starlightk7/OpenSFC/Sound Modules/TCMK-77XR F/Rev B/TCMK-77XR.kicad_sch

## KiCad design Sound Modules/TCMK-77XR F/Rev B/TCMK-77XR.kicad_sch (2026-03-24)

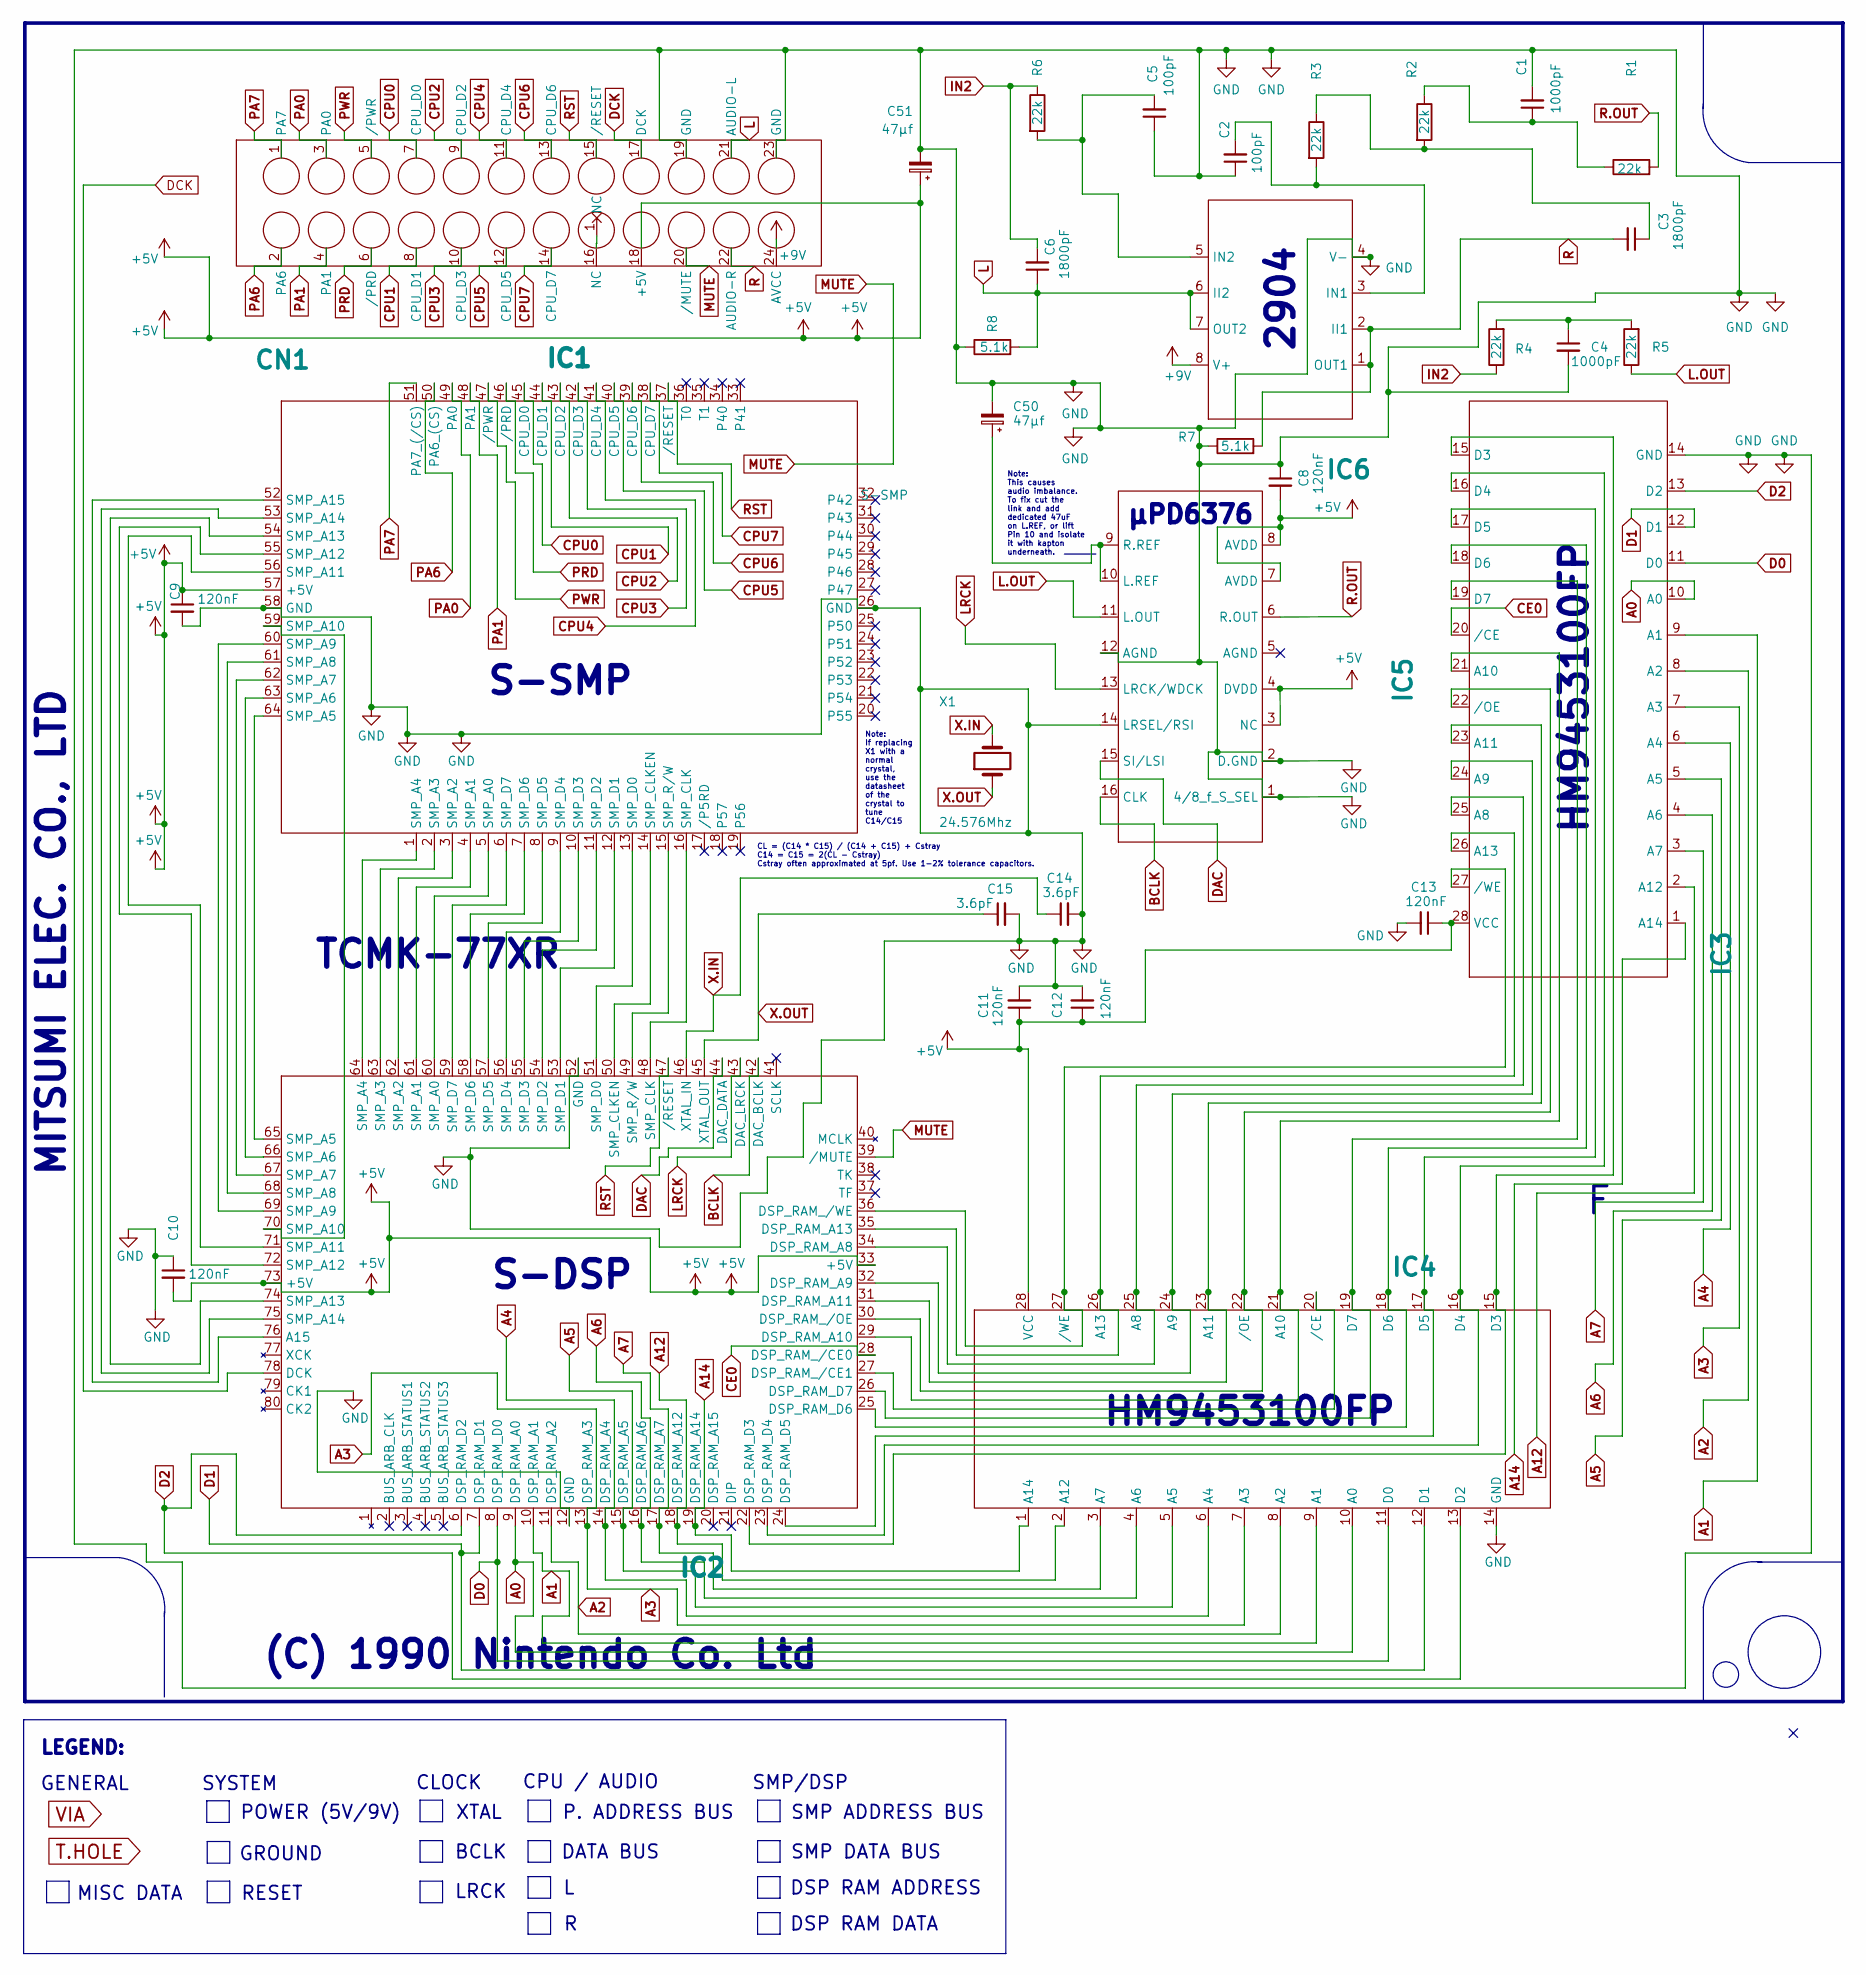
[picture p21: schematic TCMK-77XR.kicad_sch]

Parts:
C1, C4: 1000pF; C_0805_2012Metric
C2, C5: 100pF; C_0805_2012Metric
C3, C6: 1800pF; C_0805_2012Metric
C8, C9, C10, C11, C12, C13: 120nF; C_0805_2012Metric
C14, C15: 3.6pF; C_0805_2012Metric
C50, C51: 47µf; C_Radial_D6.3mm_H5.0mm_P2.50mm
CN1: 2x12 Connector Female; PinHeader_2x12_P2.00mm_Vertical
IC1: S-SMP
IC2: S-DSP
IC3, IC4: HM9453100FP; SOP-28_8.4x18.16mm_P1.27mm
IC5: µPD6376; SOIC-16W_7.5x10.3mm_P1.27mm
IC6: 2904; SOIC-8_3.9x4.9mm_P1.27mm
R1, R2, R3, R4, R5, R6: 22k; R_0805_2012Metric
R7, R8: 5.1k; R_0805_2012Metric
U99: NCStub
X1: 24.576Mhz; Crystal_HC18-U_Vertical

Connections:
+5V: C8.2, C9.1, C10.2, C11.1, C12.1, C13.1, C51.1, CN1.18 (+5V), IC1.57 (+5V), IC2.33 (+5V), IC2.73 (+5V), IC3.28 (VCC), IC4.28 (VCC), IC5.3 (NC), IC5.4 (DVDD), IC5.7 (AVDD), IC5.8 (AVDD)
+9V: CN1.24 (AVCC), IC6.8 (V+)
A0: IC2.9 (DSP_RAM_A0), IC3.10 (A0), IC4.10 (A0)
A1: IC2.10 (DSP_RAM_A1), IC3.9 (A1), IC4.9 (A1)
A2: IC2.11 (DSP_RAM_A2), IC3.8 (A2), IC4.8 (A2)
A3: IC2.13 (DSP_RAM_A3), IC3.7 (A3), IC4.7 (A3)
A4: IC2.14 (DSP_RAM_A4), IC3.6 (A4), IC4.6 (A4)
A5: IC2.15 (DSP_RAM_A5), IC3.5 (A5), IC4.5 (A5)
A6: IC2.16 (DSP_RAM_A6), IC3.4 (A6), IC4.4 (A6)
A7: IC2.17 (DSP_RAM_A7), IC3.3 (A7), IC4.3 (A7)
A12: IC2.18 (DSP_RAM_A12), IC3.2 (A12), IC4.2 (A12)
A14: IC2.19 (DSP_RAM_A14), IC3.1 (A14), IC4.1 (A14)
BCLK: IC2.42 (DAC_BCLK), IC5.16 (CLK)
CE0: IC2.28 (DSP_RAM_/CE0), IC3.20 (/CE)
CPU0: CN1.7 (CPU_D0), IC1.45 (CPU_D0)
CPU1: CN1.8 (CPU_D1), IC1.44 (CPU_D1)
CPU2: CN1.9 (CPU_D2), IC1.43 (CPU_D2)
CPU3: CN1.10 (CPU_D3), IC1.42 (CPU_D3)
CPU4: CN1.11 (CPU_D4), IC1.41 (CPU_D4)
CPU5: CN1.12 (CPU_D5), IC1.40 (CPU_D5)
CPU6: CN1.13 (CPU_D6), IC1.39 (CPU_D6)
CPU7: CN1.14 (CPU_D7), IC1.38 (CPU_D7)
D0: IC2.8 (DSP_RAM_D0), IC3.11 (D0), IC4.11 (D0)
D1: IC2.7 (DSP_RAM_D1), IC3.12 (D1), IC4.12 (D1)
D2: IC2.6 (DSP_RAM_D2), IC3.13 (D2), IC4.13 (D2)
DAC: IC2.44 (DAC_DATA), IC5.15 (SI/LSI)
DCK: CN1.17 (DCK), IC2.78 (DCK)
GND: C1.2, C2.1, C4.2, C5.1, C8.1, C9.2, C10.1, C11.2, C12.2, C13.2, C14.2, C15.2, C50.2, C51.2, CN1.19 (GND), CN1.23 (GND), IC1.26 (GND), IC1.58 (GND), IC2.12 (GND), IC2.52 (GND), IC3.14 (GND), IC4.14 (GND), IC5.1 (4/8_f_S_SEL), IC5.2 (D.GND), IC5.12 (AGND), IC5.14 (LRSEL/RSI), IC6.4 (V-), R7.1, R8.1
IN2: C6.2, R4.1, R6.1
L: C6.1, CN1.21 (AUDIO-L), IC6.6 (II2), IC6.7 (OUT2), R8.2
L.OUT: IC5.11 (L.OUT), R5.1
LRCK: IC2.43 (DAC_LRCK), IC5.13 (LRCK/WDCK)
MUTE: CN1.20 (/MUTE), IC2.39 (/MUTE)
unnamed: C1.1, R1.1, R2.1
unnamed: C2.2, IC6.3 (IN1), R3.2
unnamed: C3.1, R2.2, R3.1
unnamed: C4.1, R4.2, R5.2
unnamed: C5.2, IC6.5 (IN2), R6.2
unnamed: C50.1, IC5.9 (R.REF), IC5.10 (L.REF)
unnamed: CN1.16 (NC), U99.1
unnamed: IC1.1 (SMP_A4), IC2.64 (SMP_A4)
unnamed: IC1.2 (SMP_A3), IC2.63 (SMP_A3)
unnamed: IC1.3 (SMP_A2), IC2.62 (SMP_A2)
unnamed: IC1.4 (SMP_A1), IC2.61 (SMP_A1)
unnamed: IC1.5 (SMP_A0), IC2.60 (SMP_A0)
unnamed: IC1.6 (SMP_D7), IC2.59 (SMP_D7)
unnamed: IC1.7 (SMP_D6), IC2.58 (SMP_D6)
unnamed: IC1.8 (SMP_D5), IC2.57 (SMP_D5)
unnamed: IC1.9 (SMP_D4), IC2.56 (SMP_D4)
unnamed: IC1.10 (SMP_D3), IC2.55 (SMP_D3)
unnamed: IC1.11 (SMP_D2), IC2.54 (SMP_D2)
unnamed: IC1.12 (SMP_D1), IC2.53 (SMP_D1)
unnamed: IC1.13 (SMP_D0), IC2.51 (SMP_D0)
unnamed: IC1.14 (SMP_CLKEN), IC2.50 (SMP_CLKEN)
unnamed: IC1.15 (SMP_R/W), IC2.49 (SMP_R/W)
unnamed: IC1.16 (SMP_CLK), IC2.48 (SMP_CLK)
unnamed: IC1.52 (SMP_A15), IC2.76 (A15)
unnamed: IC1.53 (SMP_A14), IC2.75 (SMP_A14)
unnamed: IC1.54 (SMP_A13), IC2.74 (SMP_A13)
unnamed: IC1.55 (SMP_A12), IC2.72 (SMP_A12)
unnamed: IC1.56 (SMP_A11), IC2.71 (SMP_A11)
unnamed: IC1.59 (SMP_A10), IC2.70 (SMP_A10)
unnamed: IC1.60 (SMP_A9), IC2.69 (SMP_A9)
unnamed: IC1.61 (SMP_A8), IC2.68 (SMP_A8)
unnamed: IC1.62 (SMP_A7), IC2.67 (SMP_A7)
unnamed: IC1.63 (SMP_A6), IC2.66 (SMP_A6)
unnamed: IC1.64 (SMP_A5), IC2.65 (SMP_A5)
unnamed: IC2.22 (DSP_RAM_D3), IC3.15 (D3), IC4.15 (D3)
unnamed: IC2.23 (DSP_RAM_D4), IC3.16 (D4), IC4.16 (D4)
unnamed: IC2.24 (DSP_RAM_D5), IC3.17 (D5), IC4.17 (D5)
unnamed: IC2.25 (DSP_RAM_D6), IC3.18 (D6), IC4.18 (D6)
unnamed: IC2.26 (DSP_RAM_D7), IC3.19 (D7), IC4.19 (D7)
unnamed: IC2.27 (DSP_RAM_/CE1), IC4.20 (/CE)
unnamed: IC2.29 (DSP_RAM_A10), IC3.21 (A10), IC4.21 (A10)
unnamed: IC2.30 (DSP_RAM_/OE), IC3.22 (/OE), IC4.22 (/OE)
unnamed: IC2.31 (DSP_RAM_A11), IC3.23 (A11), IC4.23 (A11)
unnamed: IC2.32 (DSP_RAM_A9), IC3.24 (A9), IC4.24 (A9)
unnamed: IC2.34 (DSP_RAM_A8), IC3.25 (A8), IC4.25 (A8)
unnamed: IC2.35 (DSP_RAM_A13), IC3.26 (A13), IC4.26 (A13)
unnamed: IC2.36 (DSP_RAM_/WE), IC3.27 (/WE), IC4.27 (/WE)
PA0: CN1.3 (PA0), IC1.49 (PA0)
PA1: CN1.4 (PA1), IC1.48 (PA1)
PA6: CN1.2 (PA6), IC1.50 (PA6_(CS))
PA7: CN1.1 (PA7), IC1.51 (PA7_(/CS))
PRD: CN1.6 (/PRD), IC1.46 (/PRD)
PWR: CN1.5 (/PWR), IC1.47 (/PWR)
R: C3.2, CN1.22 (AUDIO-R), IC6.1 (OUT1), IC6.2 (II1), R7.2
R.OUT: IC5.6 (R.OUT), R1.2
RST: CN1.15 (/RESET), IC1.37 (/RESET), IC2.47 (/RESET)
X.IN: C14.1, IC2.46 (XTAL_IN), X1.2
X.OUT: C15.1, IC2.45 (XTAL_OUT), X1.1

Notes on the sheet:
SMP ADDRESS BUS
MITSUMI ELEC. CO., LTD
S-DSP
TCMK-77XR
XTAL
(C) 1990 Nintendo Co. Ltd
HM9453100FP
DSP RAM DATA
GROUND
P. ADDRESS BUS
LEGEND:
DATA BUS
LRCK
BCLK
CPU / AUDIO
RESET
SMP/DSP
SYSTEM
CLOCK
MISC DATA
DSP RAM ADDRESS
GENERAL
Note: If replacing X1 with a normal crystal, use the datasheet of the crystal to tune C14/C15
CL = (C14 * C15) / (C14 + C15) + Cstray C14 = C15 = 2(CL - Cstray) Cstray often approximated at 5pf. Use 1-2% tolerance capacitors.
2904
S-SMP
µPD6376
POWER (5V/9V)
Note: This causes audio imbalance. To fix cut the link and add dedicated 47uF on L.REF, or lift Pin 10 and isolate it with kapton underneath.
SMP DATA BUS
